Aidan-OS/Whimsy/Images/Discord Emotes/Whoopsy_P.png

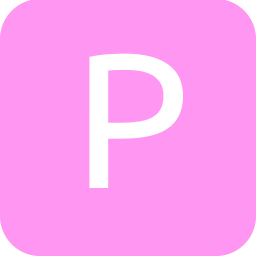
Images/Discord Emotes/Whoopsy_P.png
