Aidan-OS/Whimsy/Images/Discord Emotes/Whoopsy_S.png

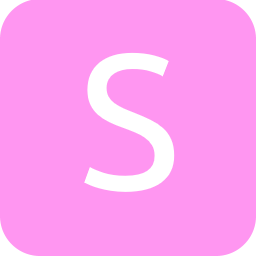
Images/Discord Emotes/Whoopsy_S.png
