Aidan-OS/Whimsy/PCB/Whimsy.kicad_sch

## KiCad design PCB/Whimsy.kicad_sch (2021-11-13)

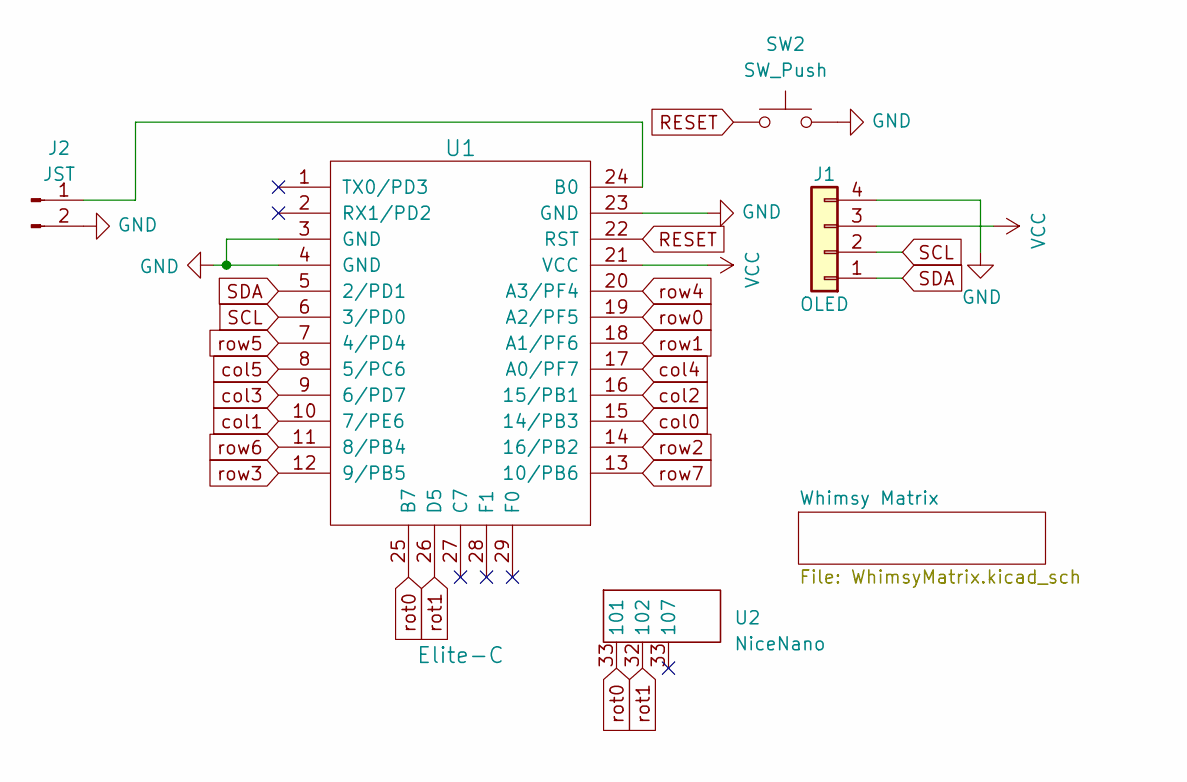
[picture p16: schematic Whimsy.kicad_sch]

Parts:
J1: OLED; OLED_4Pin
J2: JST; JST_PH_S2B-PH-K_1x02_P2.00mm_Horizontal
SW2: SW_Push; SW_Tactile_SPST_Angled_MJTP1117
U1: Elite-C; Elite-C-NoSilk
U2: NiceNano; nice_nano

Connections:
GND: J1.4, J2.2, SW2.2, U1.3 (GND), U1.4 (GND), U1.23 (GND)
unnamed: J2.1, U1.24 (B0)
RESET: SW2.1, U1.22 (RST)
SCL: J1.2, U1.6 (3/PD0)
SDA: J1.1, U1.5 (2/PD1)
VCC: J1.3, U1.21 (VCC)
col0: U1.15 (14/PB3)
col1: U1.10 (7/PE6)
col2: U1.16 (15/PB1)
col3: U1.9 (6/PD7)
col4: U1.17 (A0/PF7)
col5: U1.8 (5/PC6)
rot0: U1.25 (B7), U2.33 (101)
rot1: U1.26 (D5), U2.32 (102)
row0: U1.19 (A2/PF5)
row1: U1.18 (A1/PF6)
row2: U1.14 (16/PB2)
row3: U1.12 (9/PB5)
row4: U1.20 (A3/PF4)
row5: U1.7 (4/PD4)
row6: U1.11 (8/PB4)
row7: U1.13 (10/PB6)
