Aidan-OS/Whimsy/PCB/WhimsyMatrix.kicad_sch

## KiCad design PCB/WhimsyMatrix.kicad_sch (2021-11-13)

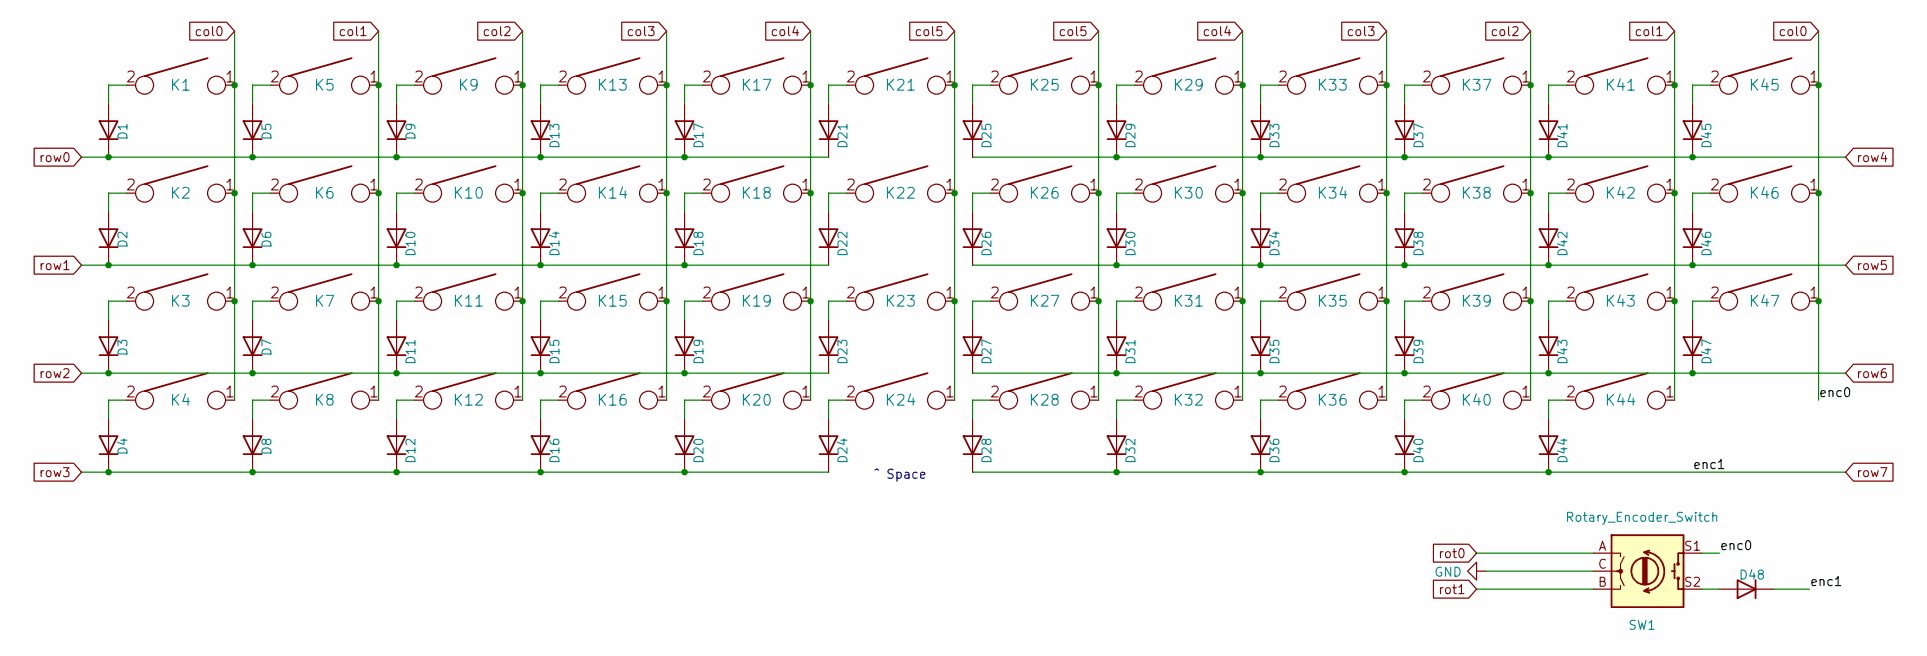
[picture p17: schematic WhimsyMatrix.kicad_sch]

Parts:
D1, D2, D3, D4, D5, D6, D7, D8, D9, D10, D11, D12, D13, D14, D15, D16, D17, D18, D19, D20, D21, D22, D23, D24, D25, D26, D27, D28, D29, D30, D31, D32, D33, D34, D35, D36, D37, D38, D39, D40, D41, D42, D43, D44, D45, D46, D47, D48: D; Diode-Hybrid-Back
K1, K4, K5, K6, K7, K8, K9, K10, K11, K12, K13, K14, K15, K16, K17, K18, K19, K21, K22, K23, K25, K26, K27, K29, K30, K31, K32, K33, K34, K35, K36, K37, K38, K39, K40, K41, K42, K43, K44, K47: KEYSW; MXOnly-1U-NoLED
K2, K20, K28, K46: KEYSW; MXOnly-1.25U-NoLED
K3, K45: KEYSW; MXOnly-1.5U-NoLED
K24: KEYSW; MXOnly-2U-ReversedStabilizers-NoLED
SW1: Rotary_Encoder_Switch; RotaryEncoder_Alps_EC11E-Switch_Vertical_H20mm-keebio_modif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

Connections:
GND: SW1.C
unnamed: D1.2 (A), K1.2
unnamed: D2.2 (A), K2.2
unnamed: D3.2 (A), K3.2
unnamed: D4.2 (A), K4.2
unnamed: D5.2 (A), K5.2
unnamed: D6.2 (A), K6.2
unnamed: D7.2 (A), K7.2
unnamed: D8.2 (A), K8.2
unnamed: D9.2 (A), K9.2
unnamed: D10.2 (A), K10.2
unnamed: D11.2 (A), K11.2
unnamed: D12.2 (A), K12.2
unnamed: D13.2 (A), K13.2
unnamed: D14.2 (A), K14.2
unnamed: D15.2 (A), K15.2
unnamed: D16.2 (A), K16.2
unnamed: D17.2 (A), K17.2
unnamed: D18.2 (A), K18.2
unnamed: D19.2 (A), K19.2
unnamed: D20.2 (A), K20.2
unnamed: D21.2 (A), K21.2
unnamed: D22.2 (A), K22.2
unnamed: D23.2 (A), K23.2
unnamed: D24.2 (A), K24.2
unnamed: D25.2 (A), K25.2
unnamed: D26.2 (A), K26.2
unnamed: D27.2 (A), K27.2
unnamed: D28.2 (A), K28.2
unnamed: D29.2 (A), K29.2
unnamed: D30.2 (A), K30.2
unnamed: D31.2 (A), K31.2
unnamed: D32.2 (A), K32.2
unnamed: D33.2 (A), K33.2
unnamed: D34.2 (A), K34.2
unnamed: D35.2 (A), K35.2
unnamed: D36.2 (A), K36.2
unnamed: D37.2 (A), K37.2
unnamed: D38.2 (A), K38.2
unnamed: D39.2 (A), K39.2
unnamed: D40.2 (A), K40.2
unnamed: D41.2 (A), K41.2
unnamed: D42.2 (A), K42.2
unnamed: D43.2 (A), K43.2
unnamed: D44.2 (A), K44.2
unnamed: D45.2 (A), K45.2
unnamed: D46.2 (A), K46.2
unnamed: D47.2 (A), K47.2
unnamed: D48.2 (A), SW1.S2
col0: K1.1, K2.1, K3.1, K4.1, K45.1, K46.1, K47.1, SW1.S1
col1: K5.1, K6.1, K7.1, K8.1, K41.1, K42.1, K43.1, K44.1
col2: K9.1, K10.1, K11.1, K12.1, K37.1, K38.1, K39.1, K40.1
col3: K13.1, K14.1, K15.1, K16.1, K33.1, K34.1, K35.1, K36.1
col4: K17.1, K18.1, K19.1, K20.1, K29.1, K30.1, K31.1, K32.1
col5: K21.1, K22.1, K23.1, K24.1, K25.1, K26.1, K27.1, K28.1
rot0: SW1.A
rot1: SW1.B
row0: D1.1 (K), D5.1 (K), D9.1 (K), D13.1 (K), D17.1 (K), D21.1 (K)
row1: D2.1 (K), D6.1 (K), D10.1 (K), D14.1 (K), D18.1 (K), D22.1 (K)
row2: D3.1 (K), D7.1 (K), D11.1 (K), D15.1 (K), D19.1 (K), D23.1 (K)
row3: D4.1 (K), D8.1 (K), D12.1 (K), D16.1 (K), D20.1 (K), D24.1 (K)
row4: D25.1 (K), D29.1 (K), D33.1 (K), D37.1 (K), D41.1 (K), D45.1 (K)
row5: D26.1 (K), D30.1 (K), D34.1 (K), D38.1 (K), D42.1 (K), D46.1 (K)
row6: D27.1 (K), D31.1 (K), D35.1 (K), D39.1 (K), D43.1 (K), D47.1 (K)
row7: D28.1 (K), D32.1 (K), D36.1 (K), D40.1 (K), D44.1 (K), D48.1 (K)

Notes on the sheet:
^ Space
